AriaSalvatrice/Aria-CMOS-Synth/4040 Breakout Board/4040.png

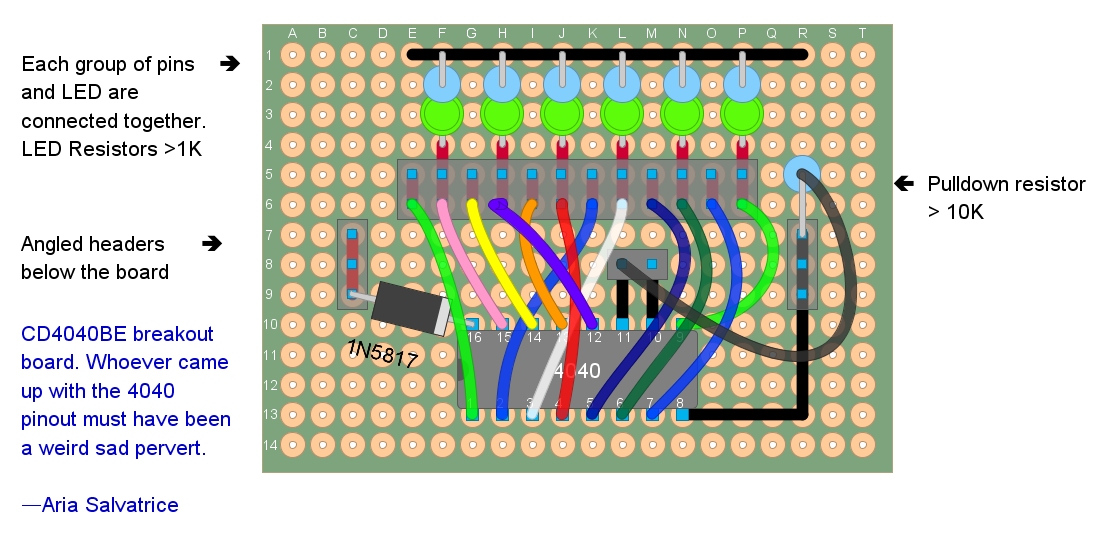
4040 Breakout Board/4040.png
