AriaSalvatrice/Aria-CMOS-Synth/40106 Oscillators/40106 Layout.png

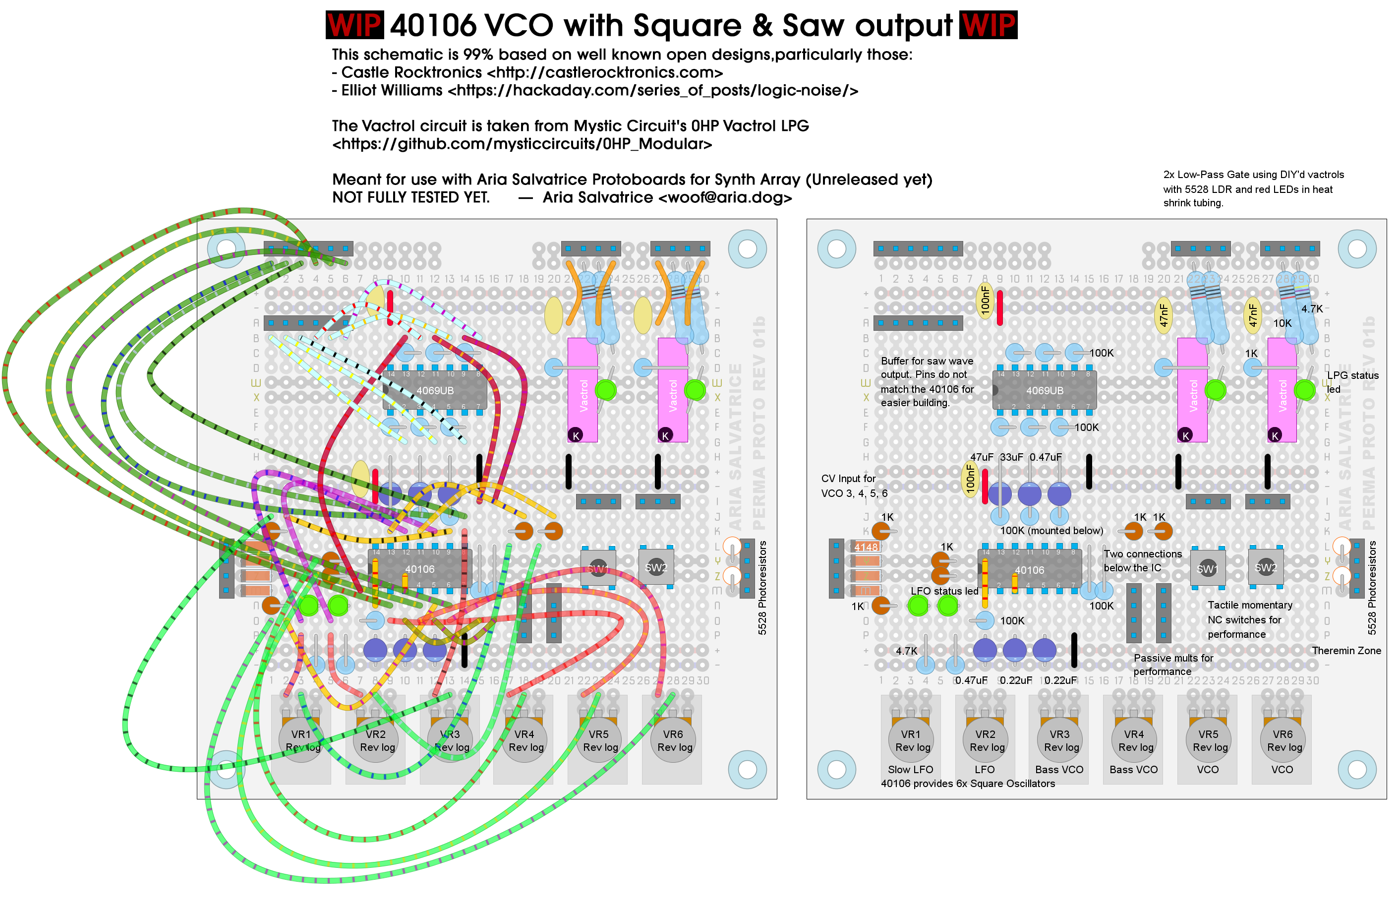
40106 Oscillators/40106 Layout.png
