AriaSalvatrice/Aria-CMOS-Synth/Output Module/Output Module Layout.png

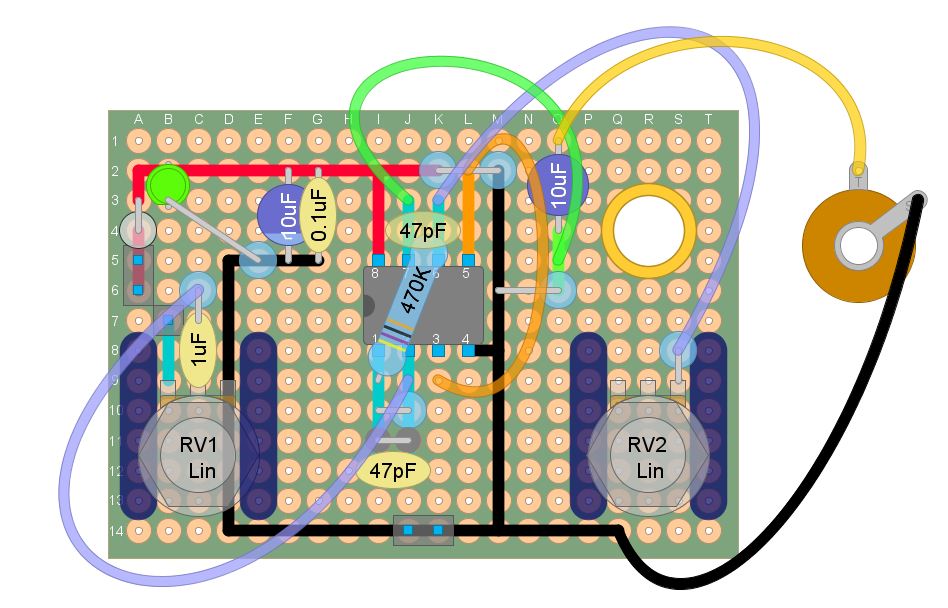
Output Module/Output Module Layout.png
