AriaSalvatrice/Aria-CMOS-Synth/Percussions and Switching Sequencer Module/Percussions and Switching Sequencer Layout (Wires).png

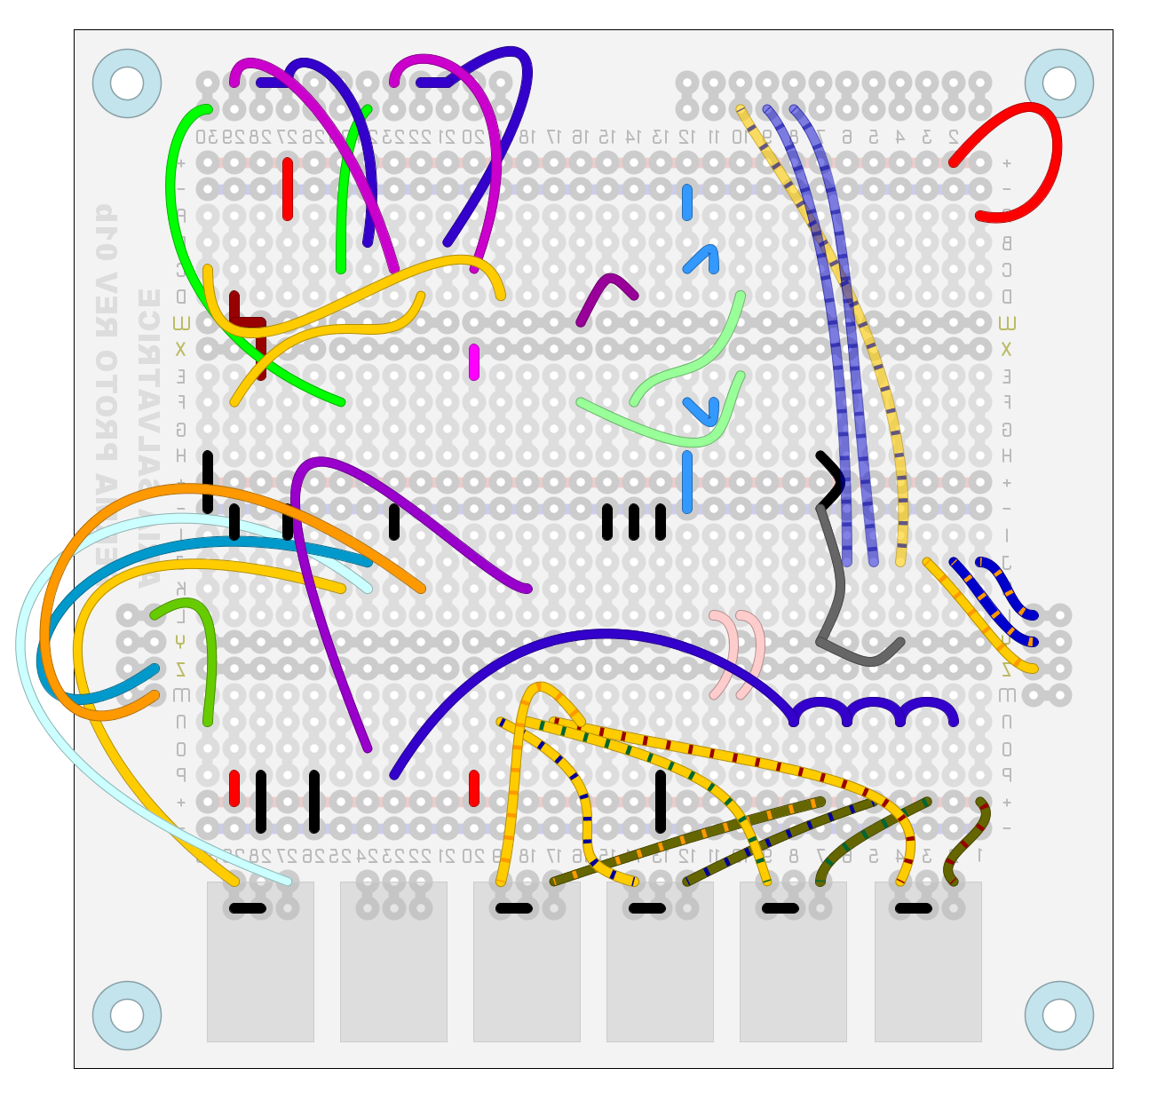
Percussions and Switching Sequencer Module/Percussions and Switching Sequencer Layout (Wires).png
