AriaSalvatrice/Aria-CMOS-Synth/Percussions and Switching Sequencer Module/Percussions and Switching Sequencer Layout.png

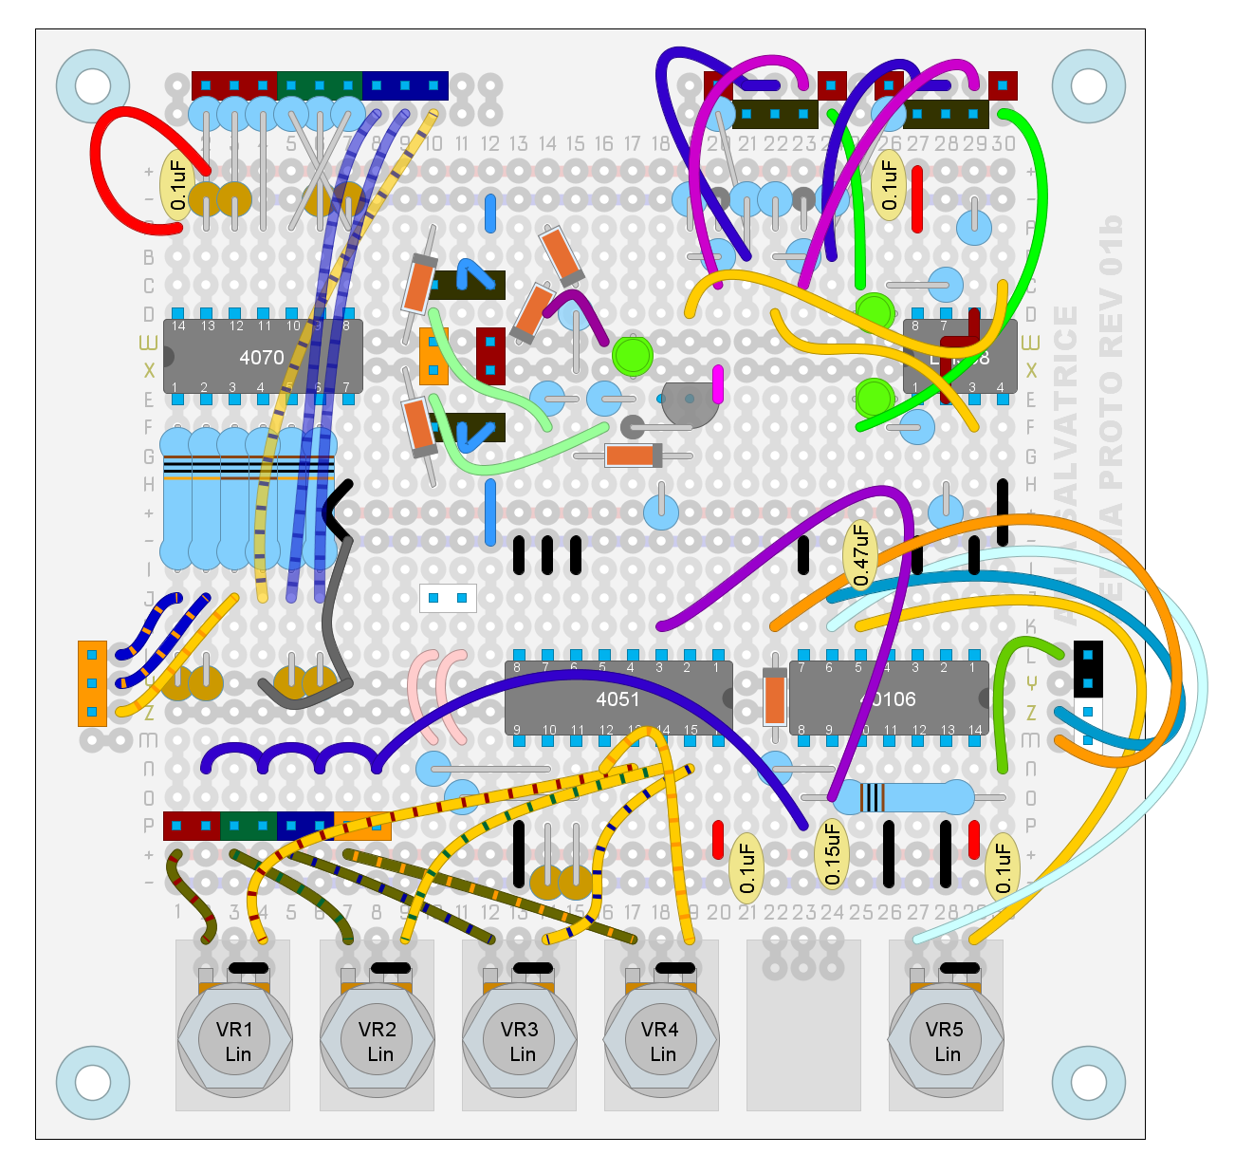
Percussions and Switching Sequencer Module/Percussions and Switching Sequencer Layout.png
